s7a73farm/s7a73farm_Party_Badge_DC26/firmware/color.h

/***********************************************************************
* FILENAME: color.h 
* AUTHOR: s7a73farm, gr3yR0n1n
* DATE: 07.07.2018
*
* Copyright s7a73farm 2018.  All rights reserved.
***********************************************************************/


#ifndef COLOR_H 
#define COLOR_H 


// RGB Colors
typedef struct color_t {
    unsigned char r;
    unsigned char g;
    unsigned char b;
} color;


extern const color blue;




#endif
